youcifer13/Practical-Data-Measurment-Systems-and-Sensors-Project/Readings and Testing/2.jpeg

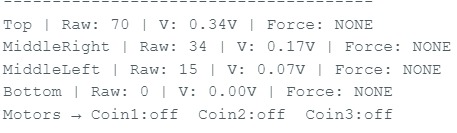
Readings and Testing/2.jpeg
