youcifer13/Practical-Data-Measurment-Systems-and-Sensors-Project/Readings and Testing/8.jpeg

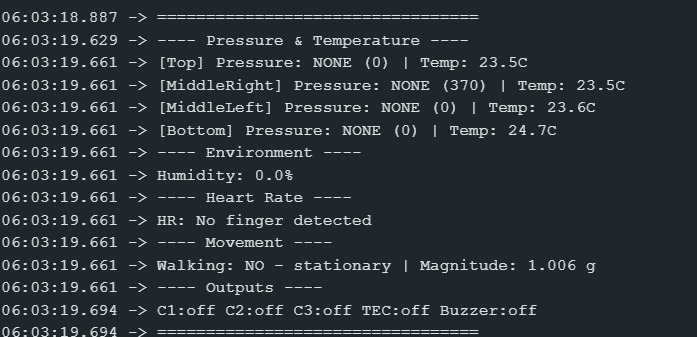
Readings and Testing/8.jpeg
